nocoolnicksleft/roco-kato-adapter/stl/Roco_Turnout_L_2417.stl

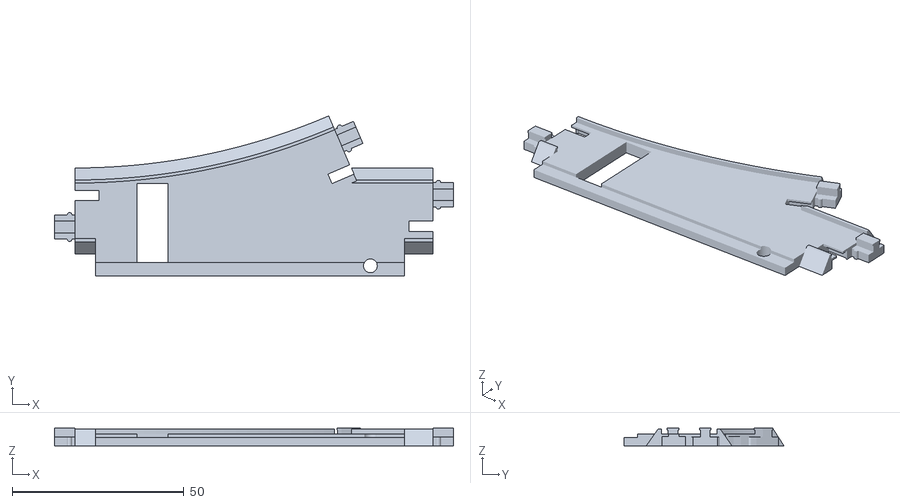
[picture p45: CAD file, 2026-04-19]
stl/Roco_Turnout_L_2417.stl
116.2 x 46.7 x 5.20
