nocoolnicksleft/roco-kato-adapter/stl/Roco_Straight_2426_17.2mm.stl

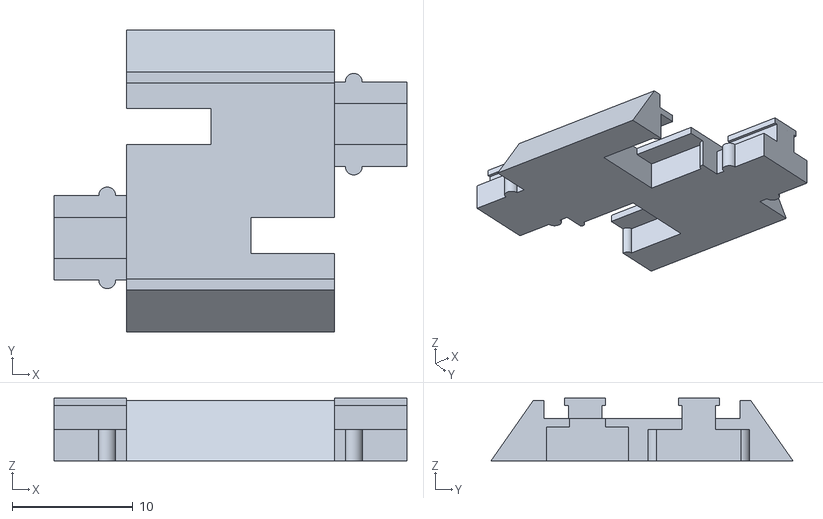
[picture p46: CAD file, 2026-04-19]
stl/Roco_Straight_2426_17.2mm.stl
29.2 x 25.0 x 5.20
