nocoolnicksleft/roco-kato-adapter/stl/Roco_Curve_2410S_R3A_30.stl

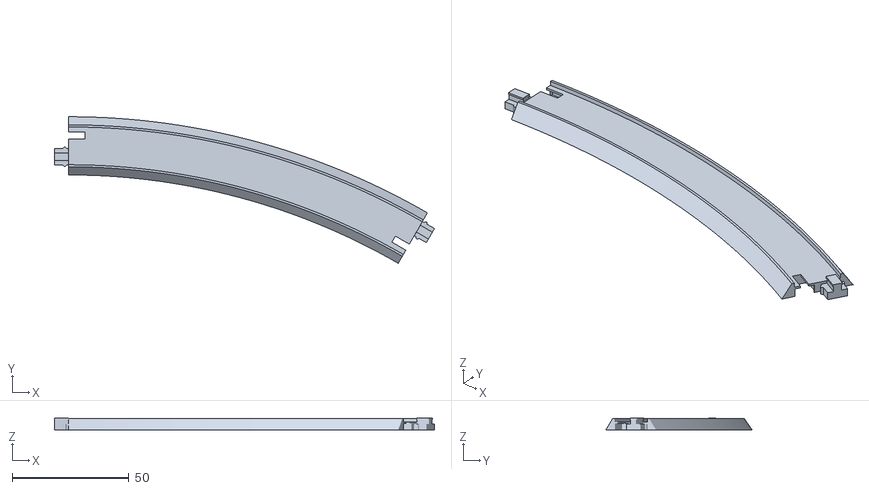
[picture p47: CAD file, 2026-04-19]
stl/Roco_Curve_2410S_R3A_30.stl
163.0 x 62.9 x 5.20
