nocoolnicksleft/roco-kato-adapter/stl/Roco_Straight_2421_50.0mm.stl

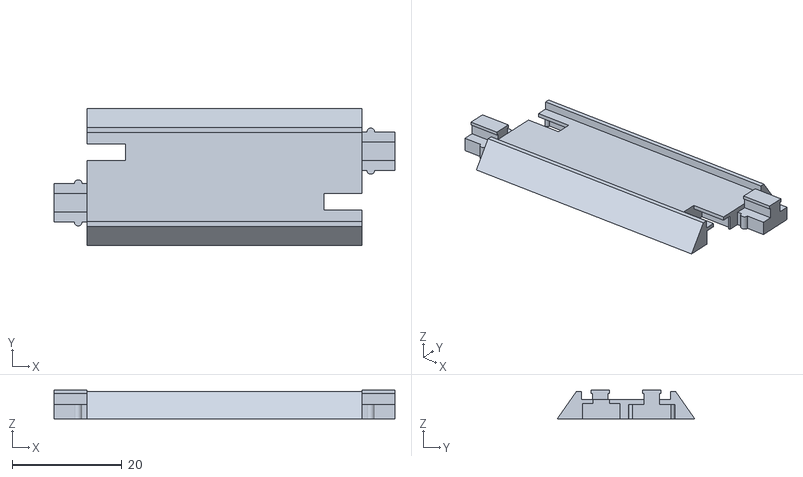
[picture p48: CAD file, 2026-04-19]
stl/Roco_Straight_2421_50.0mm.stl
62.0 x 25.0 x 5.20
