nocoolnicksleft/roco-kato-adapter/stl/Roco_Curve_2405_R6_15.stl

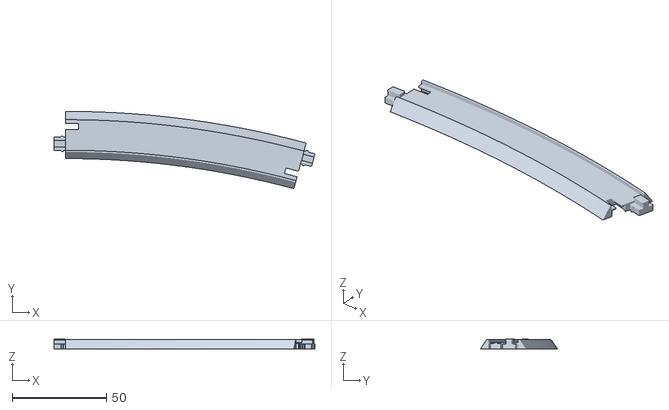
[picture p49: CAD file, 2026-04-19]
stl/Roco_Curve_2405_R6_15.stl
138.2 x 40.9 x 5.20
