nocoolnicksleft/roco-kato-adapter/stl/Roco_Turnout_L_2417_w_Roco_Curve_2420_R1_24.stl

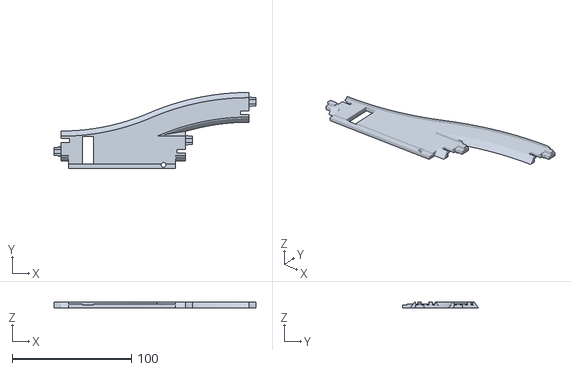
[picture p50: CAD file, 2026-04-19]
stl/Roco_Turnout_L_2417_w_Roco_Curve_2420_R1_24.stl
169.6 x 63.8 x 5.20
