nocoolnicksleft/roco-kato-adapter/stl/Roco_Straight_2423_54.2mm.stl

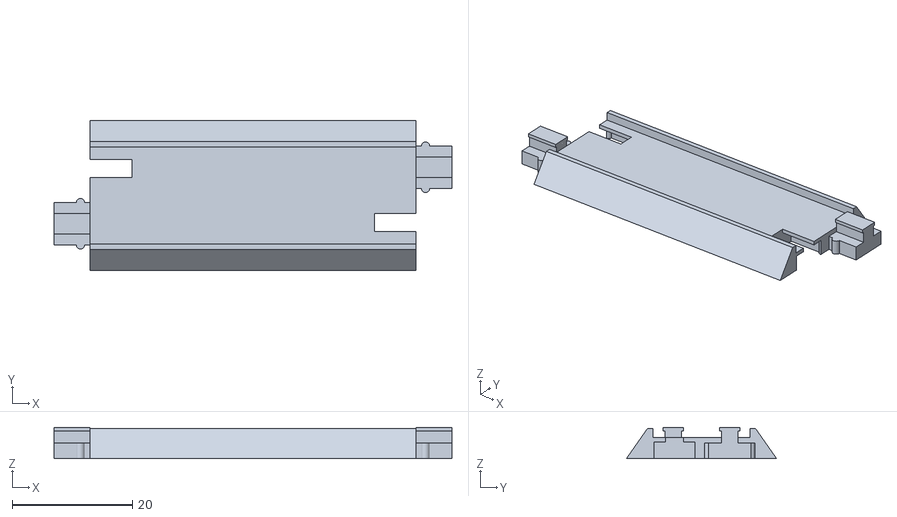
[picture p51: CAD file, 2026-04-19]
stl/Roco_Straight_2423_54.2mm.stl
66.2 x 25.0 x 5.20
