nocoolnicksleft/roco-kato-adapter/stl/Roco_Turnout_R_2418.stl

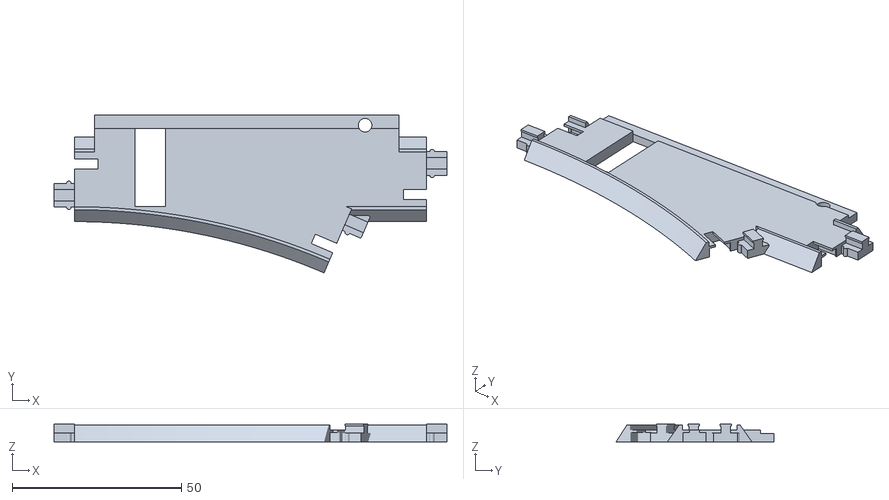
[picture p52: CAD file, 2026-04-19]
stl/Roco_Turnout_R_2418.stl
116.2 x 46.7 x 5.20
