nocoolnicksleft/roco-kato-adapter/stl/Roco_Curve_2408_R5_15.stl

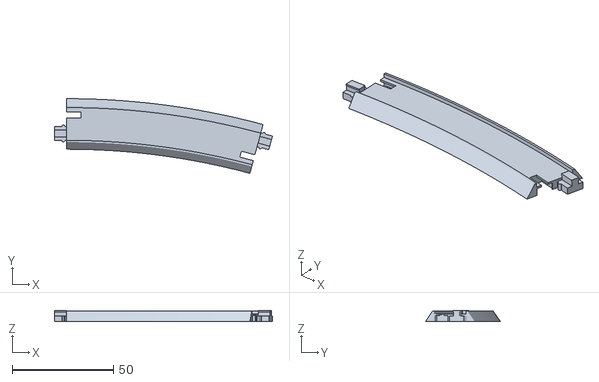
[picture p53: CAD file, 2026-04-19]
stl/Roco_Curve_2408_R5_15.stl
107.8 x 36.9 x 5.20
