nocoolnicksleft/roco-kato-adapter/stl/Roco_Curve_2420_R1_24.stl

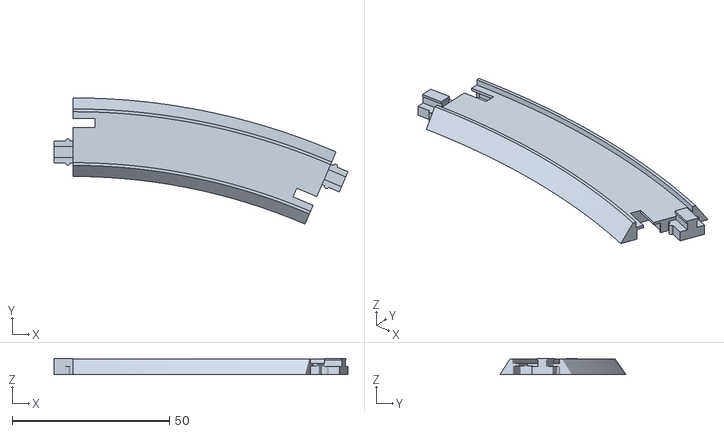
[picture p54: CAD file, 2026-04-19]
stl/Roco_Curve_2420_R1_24.stl
93.5 x 40.2 x 5.20
