nocoolnicksleft/roco-kato-adapter/stl/Roco_Curve_2420_R1_6.stl

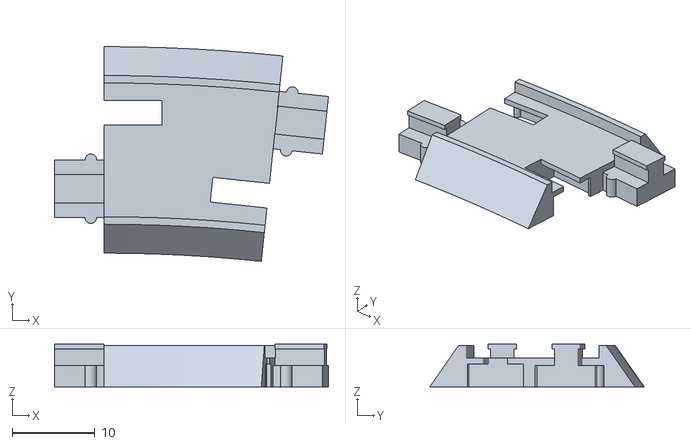
[picture p55: CAD file, 2026-04-19]
stl/Roco_Curve_2420_R1_6.stl
33.2 x 26.0 x 5.20
