nocoolnicksleft/roco-kato-adapter/stl/Roco_Curve_2407_R4_15.stl

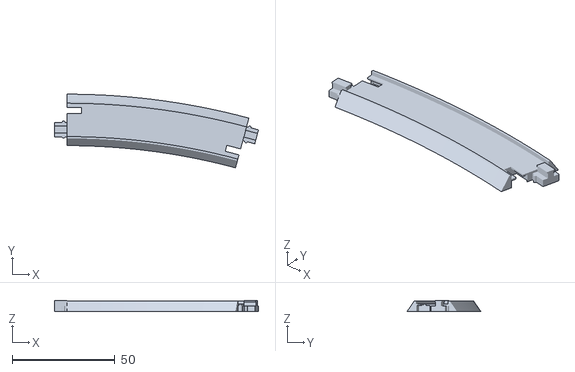
[picture p56: CAD file, 2026-04-19]
stl/Roco_Curve_2407_R4_15.stl
99.1 x 35.8 x 5.20
