nocoolnicksleft/roco-kato-adapter/stl/Roco_Curve_2409S_R3A_15.stl

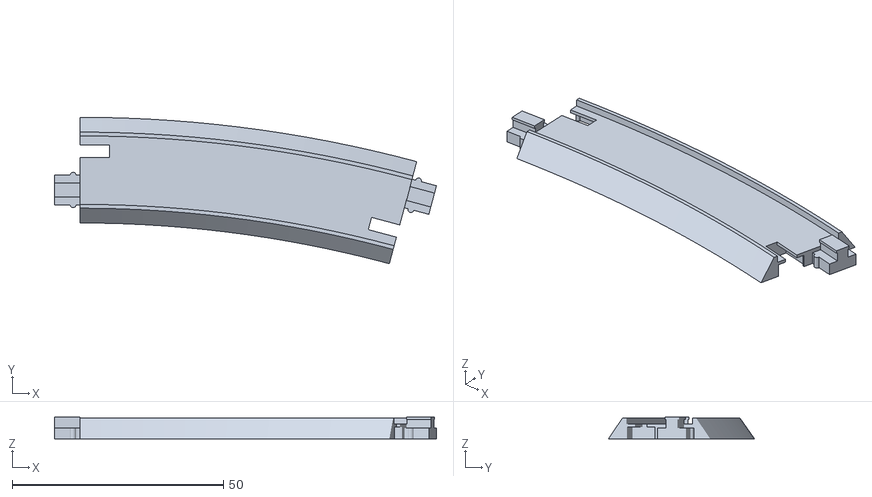
[picture p57: CAD file, 2026-04-19]
stl/Roco_Curve_2409S_R3A_15.stl
90.4 x 34.6 x 5.20
