nocoolnicksleft/roco-kato-adapter/stl/Roco_Curve_2402_R1_30.stl

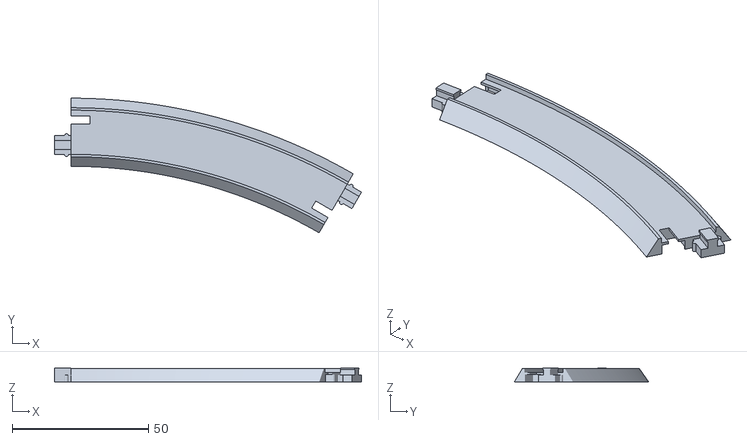
[picture p58: CAD file, 2026-04-19]
stl/Roco_Curve_2402_R1_30.stl
112.6 x 49.4 x 5.20
