nocoolnicksleft/roco-kato-adapter/stl/Sleeper_Belt_Straight_Unijoiner.stl

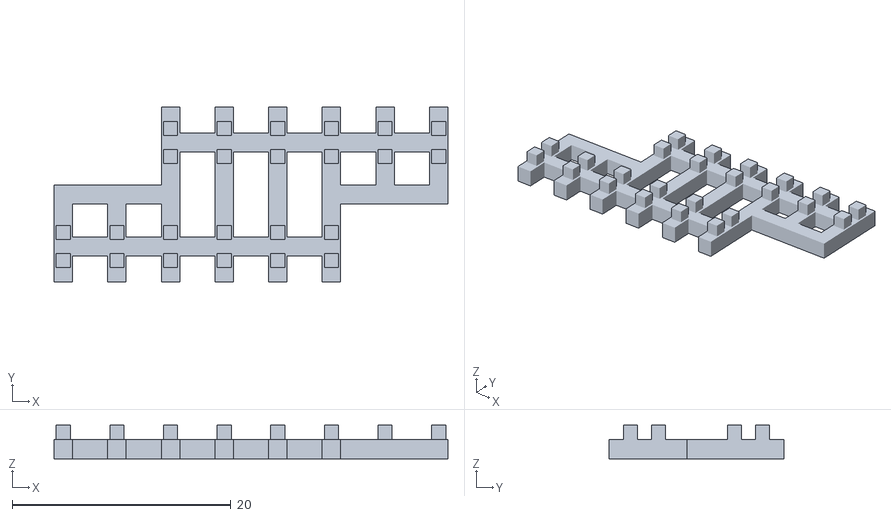
[picture p59: CAD file, 2026-04-19]
stl/Sleeper_Belt_Straight_Unijoiner.stl
36.0 x 16.0 x 3.10
