nocoolnicksleft/roco-kato-adapter/stl/Sleeper_Belt_Straight_Closed.stl

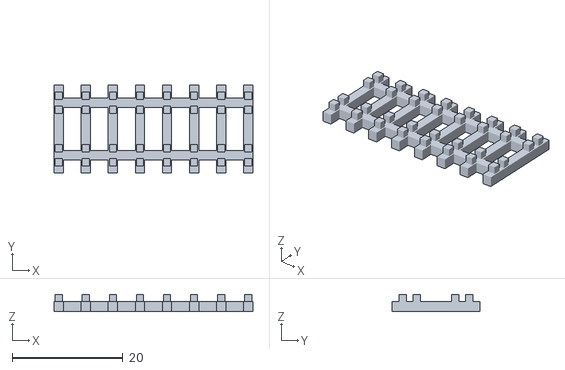
[picture p60: CAD file, 2026-04-19]
stl/Sleeper_Belt_Straight_Closed.stl
36.0 x 16.0 x 3.10
