nocoolnicksleft/roco-kato-adapter/stl/Roco_Turnout_R_2418_nojoin.stl

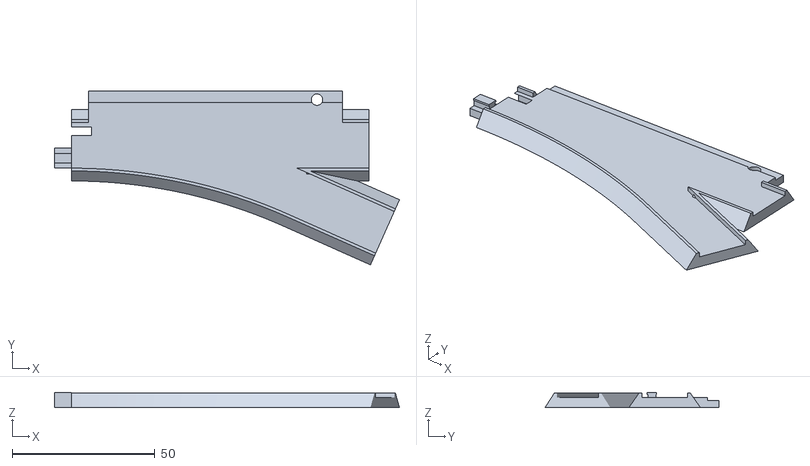
[picture p61: CAD file, 2026-04-07]
stl/Roco_Turnout_R_2418_nojoin.stl
120.9 x 60.9 x 5.20
