nocoolnicksleft/roco-kato-adapter/stl/Roco_Turnout_L_2417_nojoin.stl

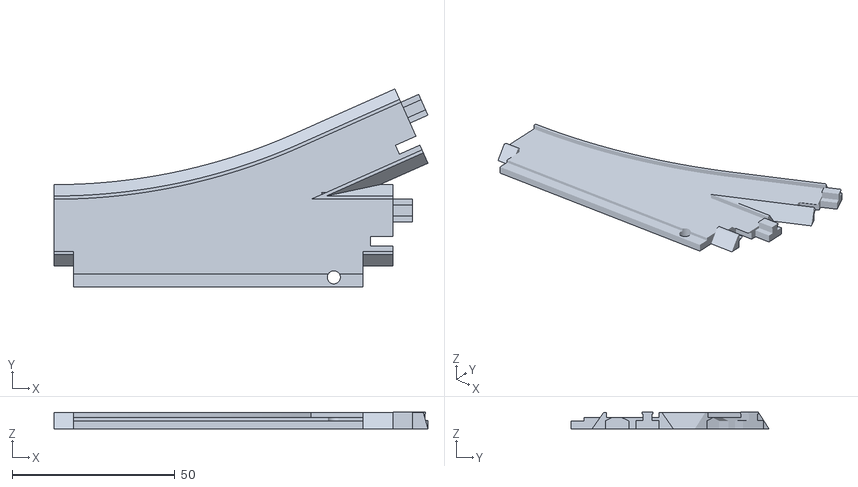
[picture p62: CAD file, 2026-04-07]
stl/Roco_Turnout_L_2417_nojoin.stl
114.9 x 60.9 x 5.20
